Griefed/LSC64/images/Social_Preview.PNG

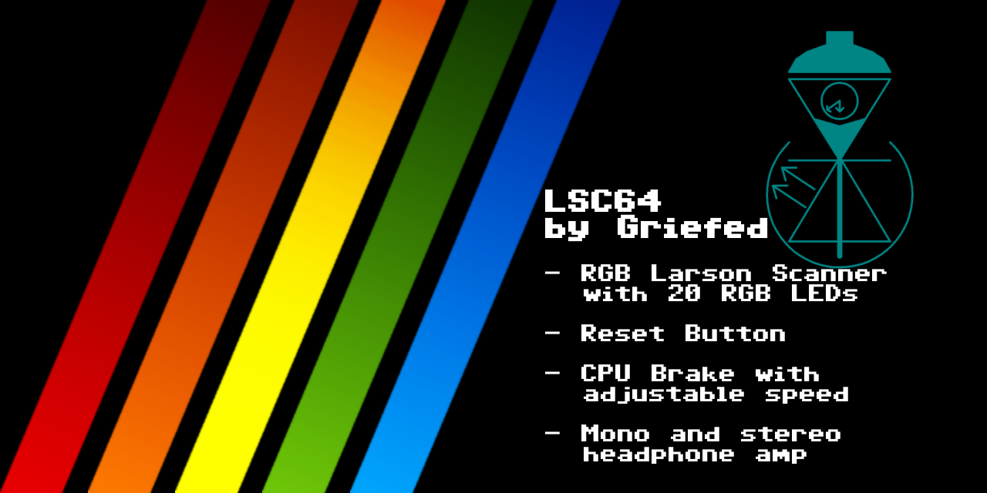
images/Social_Preview.PNG
